Rudii-25/BloodHound_VENOM/BloodHound_VENOM.kicad_sch

## KiCad design BloodHound_VENOM.kicad_sch (2026-01-19)

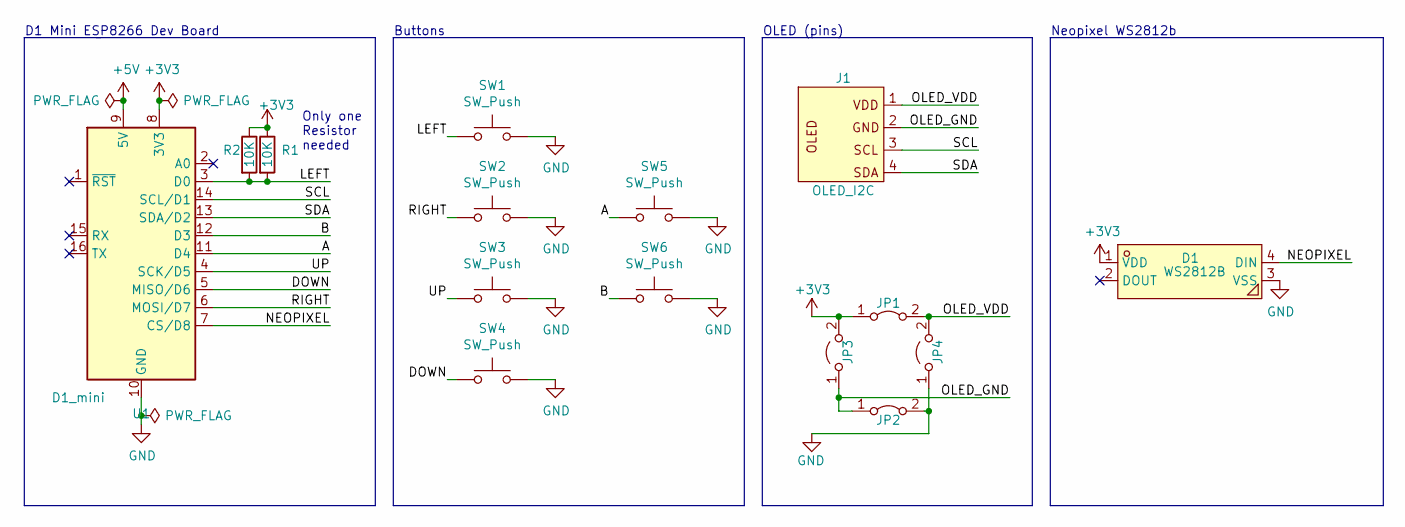
[picture p27: schematic BloodHound_VENOM.kicad_sch]

Parts:
D1: WS2812B; LED-SMD_4P-L5.0-W5.0-BL_TC5050RGB-handsolder; MPN C114586
J1: OLED_I2C; OLED_I2C_1.3
JP1, JP2: Jumper_2_Bridged; Bridge
JP3, JP4: Jumper_2_Open; SolderJumper_Open
R1: 10K; R_1206_3216Metric_Pad1.30x1.75mm_HandSolder
R2: 10K; R_Axial_DIN0204_L3.6mm_D1.6mm_P7.62mm_Horizontal
SW1, SW2, SW3, SW4, SW6: SW_Push; SW-KEY-TH_4P-L6.0-W6.0-P4.50-LS6.5; MPN C381013; LCSC Part C381013
SW5: SW_Push; SW-KEY-TH_4P-L6.0-W6.0-P4.50-LS6.5; MPN C381013
U1: D1_mini; D1_mini_ESP8266

Connections:
+3V3: D1.1 (VDD), JP1.1 (A), JP3.2 (B), R1.1, R2.1, U1.8 (3V3)
+5V: U1.9 (5V)
A: SW5.1 (A), U1.11 (D4)
B: SW6.1 (A), U1.12 (D3)
DOWN: SW4.1 (A), U1.5 (MISO/D6)
GND: D1.3 (VSS), JP2.2 (B), JP4.1 (A), SW1.2 (B), SW2.2 (B), SW3.2 (B), SW4.2 (B), SW5.2 (B), SW6.2 (B), U1.10 (GND)
LEFT: R1.2, R2.2, SW1.1 (A), U1.3 (D0)
NEOPIXEL: D1.4 (DIN), U1.7 (CS/D8)
OLED_GND: J1.2 (GND), JP2.1 (A), JP3.1 (A)
OLED_VDD: J1.1 (VDD), JP1.2 (B), JP4.2 (B)
RIGHT: SW2.1 (A), U1.6 (MOSI/D7)
SCL: J1.3 (SCL), U1.14 (SCL/D1)
SDA: J1.4 (SDA), U1.13 (SDA/D2)
UP: SW3.1 (A), U1.4 (SCK/D5)

Notes on the sheet:
OLED (pins)
D1 Mini ESP8266 Dev Board
Neopixel WS2812b
Buttons
Only one Resistor needed
