Rudii-25/BloodHound_VENOM/LiPo_Battery_Version_PCB/BloodHound_VENOM_LiPo.kicad_sch

## KiCad design LiPo_Battery_Version_PCB/BloodHound_VENOM_LiPo.kicad_sch (2025-12-24)

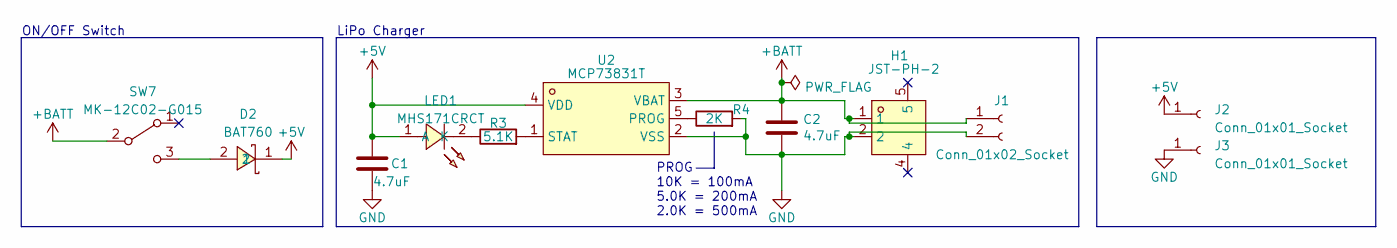
[picture p28: schematic BloodHound_VENOM_LiPo.kicad_sch]

Parts:
C1, C2: 4.7uF; C_0603_1608Metric
D2: BAT760; SOD-323_L1.8-W1.3-LS2.5-RD; MPN C116158
H1: JST-PH-2; CONN-SMD_2P-P2.00_XUNPU_WAFER-PH2.0-2PWB; MPN C3029440
J1: Conn_01x02_Socket; PinSocket_1x02_P2.54mm_Vertical
J2, J3: Conn_01x01_Socket; PinSocket_1x01_P2.54mm_Vertical
LED1: MHS171CRCT; LED-SMD_L2.0-W1.1_SIDE; MPN C693903
R3: 5.1K; R_0402_1005Metric
R4: 2K; R_0402_1005Metric
SW7: MK-12C02-G015; SW_MK-12C02-G020; MPN C2911519
U2: MCP73831T; SOT-23-5_L3.0-W1.7-P0.95-LS2.8-BL; MPN C424093

Connections:
+5V: C1.1, D2.1, J2.1, LED1.1 (A), U2.4 (VDD)
+BATT: C2.1, H1.1, J1.1, SW7.2 (B), U2.3 (VBAT)
GND: C1.2, C2.2, H1.2, J1.2, J3.1, R4.2, U2.2 (VSS)
unnamed: D2.2, SW7.3 (C)
unnamed: LED1.2 (K), R3.1
unnamed: R3.2, U2.1 (STAT)
unnamed: R4.1, U2.5 (PROG)

Notes on the sheet:
LiPo Charger
ON/OFF Switch
PROG 10K = 100mA 5.0K = 200mA 2.0K = 500mA
